wilko1971/D1-Mini-Case/Rotary Encoder/D1 Round Remix Separator Rotary Encoder.stl

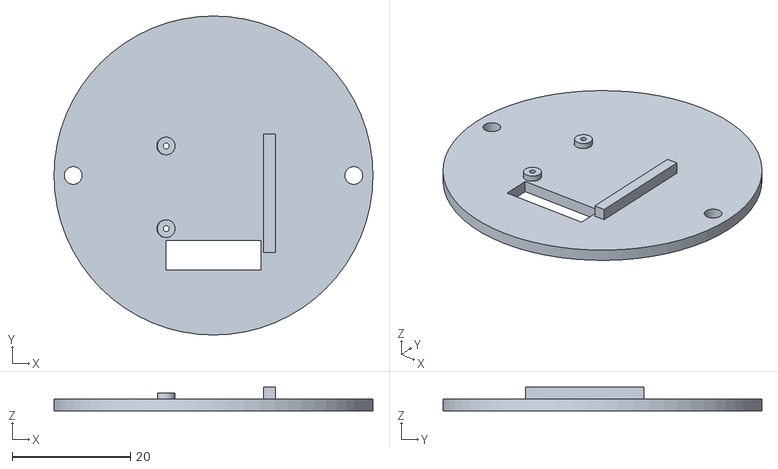
[picture p15: CAD file, 2022-03-28]
Rotary Encoder/D1 Round Remix Separator Rotary Encoder.stl
54.0 x 54.0 x 4.00
