wilko1971/D1-Mini-Case/Short Tops/D1 Round Remix Short Top.stl

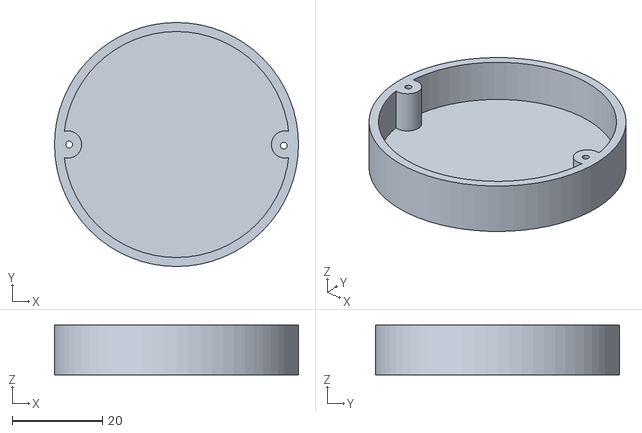
[picture p16: CAD file, 2022-03-13]
Short Tops/D1 Round Remix Short Top.stl
54.0 x 54.0 x 11.0
