wilko1971/D1-Mini-Case/Sim800L/D1 Round Remix Separator SIM800L.stl

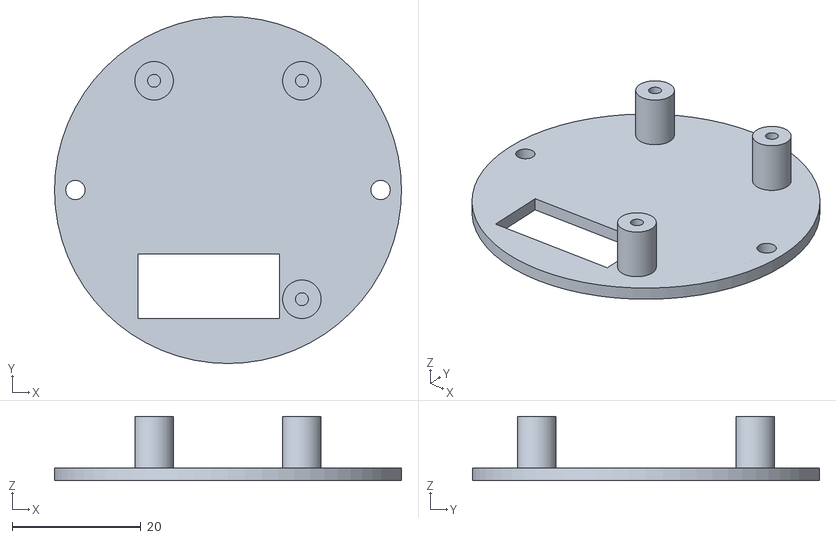
[picture p17: CAD file, 2022-03-13]
Sim800L/D1 Round Remix Separator SIM800L.stl
54.0 x 54.0 x 10.0
