wilko1971/D1-Mini-Case/Stands/D1 Remix Round  Desk Stand.stl

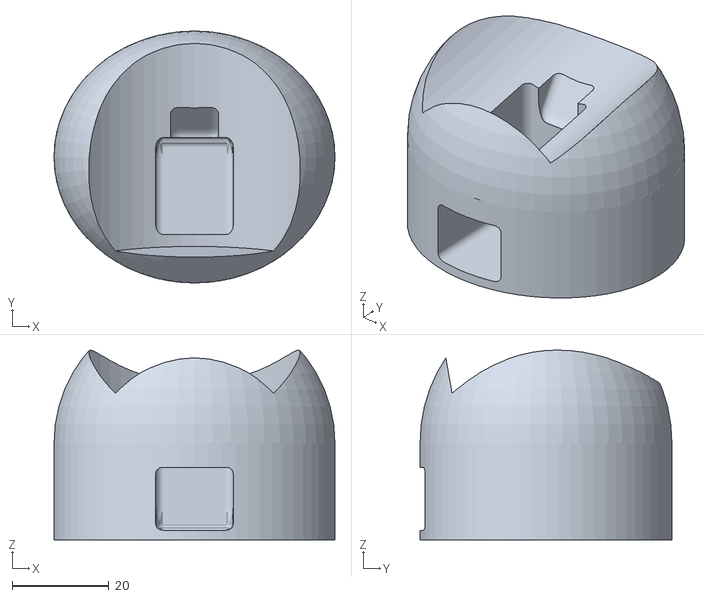
[picture p18: CAD file, 2022-03-13]
Stands/D1 Remix Round Desk Stand.stl
58.0 x 52.0 x 39.2
