wilko1971/D1-Mini-Case/Tops/D1 Round Remix Top Lines.stl

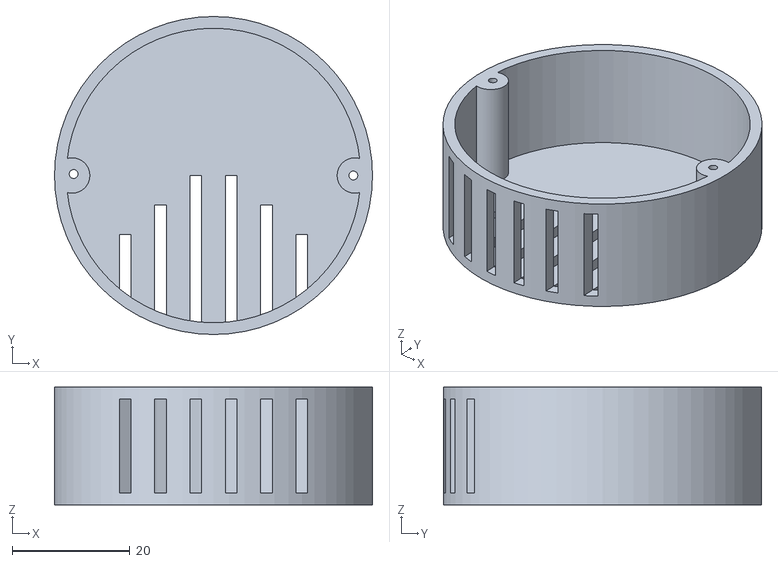
[picture p19: CAD file, 2022-03-13]
Tops/D1 Round Remix Top Lines.stl
54.0 x 54.0 x 20.0
